oelprinz-org/BL49SP/software/V0.0.3_TEST/V0.0.3_TEST.ino

/*
    Example code compatible with the Lambda Shield for Arduino.
    
    Copyright (C) 2017 - 2020 Bylund Automotive AB.

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
    Contact information of author:
    http://www.bylund-automotive.com/
    
    info@bylund-automotive.com

    Version history:
    2020-03-29        v1.0.0        First release to GitHub.
    2020-06-18        v1.1.0        Implemented support for data logging.
    2023-12-18        v1.1.1        Adaption for BL49sp.

*/

//Define included headers.
#include <SPI.h>
#include <SD.h>
#include <Wire.h>
#include <Adafruit_MCP4725.h>

Adafruit_MCP4725 MCP4725;

//Define CJ125 registers used.
#define           CJ125_IDENT_REG_REQUEST             0x4800        /* Identify request, gives revision of the chip. */
#define           CJ125_DIAG_REG_REQUEST              0x7800        /* Dignostic request, gives the current status. */
#define           CJ125_INIT_REG1_REQUEST             0x6C00        /* Requests the first init register. */
#define           CJ125_INIT_REG2_REQUEST             0x7E00        /* Requests the second init register. */
#define           CJ125_INIT_REG1_MODE_CALIBRATE      0x569D        /* Sets the first init register in calibration mode. */
#define           CJ125_INIT_REG1_MODE_NORMAL_V8      0x5688        /* Sets the first init register in operation mode. V=8 amplification. */
#define           CJ125_INIT_REG1_MODE_NORMAL_V17     0x5689        /* Sets the first init register in operation mode. V=17 amplification. */
#define           CJ125_DIAG_REG_STATUS_OK            0x28FF        /* The response of the diagnostic register when everything is ok. */
#define           CJ125_DIAG_REG_STATUS_NOPOWER       0x2855        /* The response of the diagnostic register when power is low. */
#define           CJ125_DIAG_REG_STATUS_NOSENSOR      0x287F        /* The response of the diagnostic register when no sensor is connected. */
#define           CJ125_INIT_REG1_STATUS_0            0x2888        /* The response of the init register when V=8 amplification is in use. */
#define           CJ125_INIT_REG1_STATUS_1            0x2889        /* The response of the init register when V=17 amplification is in use. */

//Define pin assignments.
#define           CJ125_NSS_PIN                       10            /* Pin used for chip select in SPI communication. */
#define           LED_STATUS_POWER                    7             /* Pin used for power the status LED, indicating we have power. */
#define           LED_STATUS_HEATER                   5             /* Pin used for the heater status LED, indicating heater activity. */
#define           HEATER_OUTPUT_PIN                   6             /* Pin used for the PWM output to the heater circuit. */
#define           ANALOG_OUTPUT_PIN                   3             /* Pin used for the PWM to the 0-1V analog output. */
#define           UB_ANALOG_INPUT_PIN                 A0            /* Analog input for power supply.*/
#define           UR_ANALOG_INPUT_PIN                 A6            /* Analog input for temperature.*/
#define           UA_ANALOG_INPUT_PIN                 A7            /* Analog input for lambda.*/
#define           EN_INPUT_PIN                      	16  	        /* Enable pin, low when engine running */

//Define adjustable parameters.
#define           SERIAL_RATE                         1             /* Serial refresh rate in HZ (1-100)*/                           
#define           UBAT_MIN                            150           /* Minimum voltage (ADC value) on Ubat to operate */

/* Define DAC MCP4725 address MCP4725A2T-E/CH */
#define DAC1_ADDR				                              0x60	        /* Address for DAC 1 chip A0 tied to GND */

/* Define DAC MCP4725 registers */
#define MCP4725_CMD_WRITEDAC			                    0x40	        /* Writes data to the DAC */
#define MCP4725_CMD_WRITEDACEEPROM		                0x60          /* Writes data to the DAC and the EEPROM (persisting the assigned value after reset) */

//Global variables.
int adcValue_UA = 0;                                                /* ADC value read from the CJ125 UA output pin */ 
int adcValue_UR = 0;                                                /* ADC value read from the CJ125 UR output pin */
int adcValue_UB = 0;                                                /* ADC value read from the voltage divider caluclating Ubat */
int adcValue_UA_Optimal = 0;                                        /* UA ADC value stored when CJ125 is in calibration mode, λ=1 */ 
int adcValue_UR_Optimal = 0;                                        /* UR ADC value stored when CJ125 is in calibration mode, optimal temperature */
int HeaterOutput = 0;                                               /* Current PWM output value (0-255) of the heater output pin */
int serial_counter = 0;                                             /* Counter used to calculate refresh rate on the serial output */
int CJ125_Status = 0;                                               /* Latest stored DIAG registry response from the CJ125 */
bool logEnabled = false;                                            /* Variable used for setting data logging enable or disabled. */
int MCP4725_value = 0;                                              /* Variable used for DAC output */


//PID regulation variables.
int dState;                                                         /* Last position input. */
int iState;                                                         /* Integrator state. */
const int iMax = 250;                                               /* Maximum allowable integrator state. */
const int iMin = -250;                                              /* Minimum allowable integrator state. */
const float pGain = 120;                                            /* Proportional gain. Default = 120*/
const float iGain = 0.8;                                            /* Integral gain. Default = 0.8*/
const float dGain = 10;                                             /* Derivative gain. Default = 10*/

//Lambda Conversion Lookup Table. (ADC 39-791).
const PROGMEM float Lambda_Conversion[753] {
  0.750, 0.751, 0.752, 0.752, 0.753, 0.754, 0.755, 0.755, 0.756, 0.757, 0.758, 0.758, 0.759, 0.760, 0.761, 0.761, 0.762, 0.763, 0.764, 0.764,
  0.765, 0.766, 0.766, 0.767, 0.768, 0.769, 0.769, 0.770, 0.771, 0.772, 0.772, 0.773, 0.774, 0.774, 0.775, 0.776, 0.777, 0.777, 0.778, 0.779,
  0.780, 0.780, 0.781, 0.782, 0.782, 0.783, 0.784, 0.785, 0.785, 0.786, 0.787, 0.787, 0.788, 0.789, 0.790, 0.790, 0.791, 0.792, 0.793, 0.793,
  0.794, 0.795, 0.796, 0.796, 0.797, 0.798, 0.799, 0.799, 0.800, 0.801, 0.802, 0.802, 0.803, 0.804, 0.805, 0.805, 0.806, 0.807, 0.808, 0.808,
  0.809, 0.810, 0.811, 0.811, 0.812, 0.813, 0.814, 0.815, 0.815, 0.816, 0.817, 0.818, 0.819, 0.820, 0.820, 0.821, 0.822, 0.823, 0.824, 0.825,
  0.825, 0.826, 0.827, 0.828, 0.829, 0.830, 0.830, 0.831, 0.832, 0.833, 0.834, 0.835, 0.836, 0.837, 0.837, 0.838, 0.839, 0.840, 0.841, 0.842,
  0.843, 0.844, 0.845, 0.846, 0.846, 0.847, 0.848, 0.849, 0.850, 0.851, 0.852, 0.853, 0.854, 0.855, 0.855, 0.856, 0.857, 0.858, 0.859, 0.860,
  0.861, 0.862, 0.863, 0.864, 0.865, 0.865, 0.866, 0.867, 0.868, 0.869, 0.870, 0.871, 0.872, 0.873, 0.874, 0.875, 0.876, 0.877, 0.878, 0.878,
  0.879, 0.880, 0.881, 0.882, 0.883, 0.884, 0.885, 0.886, 0.887, 0.888, 0.889, 0.890, 0.891, 0.892, 0.893, 0.894, 0.895, 0.896, 0.897, 0.898,
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
  14.34, 14.38, 14.41, 14.45, 14.49, 14.52, 14.56, 14.60, 14.64, 14.67, 14.71, 14.75, 14.78, 14.82, 14.86, 14.90, 14.93, 14.97, 15.01, 15.04,
  15.08, 15.12, 15.15, 15.19, 15.23, 15.26, 15.30, 15.34, 15.37, 15.41, 15.45, 15.48, 15.52, 15.56, 15.59, 15.63, 15.67, 15.70, 15.74, 15.78,
  15.81, 15.85, 15.89, 15.92, 15.96, 16.00, 16.03, 16.07, 16.11, 16.14, 16.18, 16.22, 16.25, 16.29, 16.32, 16.36, 16.40, 16.43, 16.47, 16.51,
  16.54, 16.58, 16.61, 16.65, 16.69, 16.72, 16.76, 16.79, 16.83, 16.87, 16.90, 16.94, 16.97, 17.01, 17.05, 17.08, 17.12, 17.15, 17.19, 17.22,
  17.26, 17.30, 17.33, 17.37, 17.40, 17.44, 17.47, 17.51, 17.55, 17.58, 17.62, 17.65, 17.69, 17.72, 17.76, 17.79, 17.83, 17.86, 17.90, 17.94,
  17.97, 18.01, 18.04, 18.08, 18.11, 18.15, 18.18, 18.22, 18.25, 18.29, 18.32, 18.36, 18.39, 18.43, 18.46, 18.50, 18.53, 18.57, 18.60, 18.64,
  18.67, 18.71, 18.74, 18.78, 18.81, 18.85, 18.88, 18.92, 18.95, 18.98, 19.02, 19.05, 19.09, 19.12, 19.16, 19.19, 19.23, 19.26, 19.30, 19.33,
  19.36, 19.40, 19.43, 19.47, 19.50, 19.54, 19.57, 19.60, 19.64, 19.67, 19.71, 19.74, 19.77, 19.81, 19.84, 19.88, 19.91, 19.94, 19.98, 20.01,
  20.05, 20.08, 20.11, 20.15, 20.18, 20.22, 20.25, 20.28, 20.32, 20.35, 20.38, 20.42, 20.45, 20.48, 20.52, 20.55, 20.58, 20.62, 20.65, 20.68,
  20.72, 20.75, 20.78, 20.82, 20.85, 20.88, 20.92, 20.95
};

//Function for transfering SPI data to the CJ125.
uint16_t COM_SPI(uint16_t TX_data) {

  //Configure SPI for CJ125 controller.
  SPI.setDataMode(SPI_MODE1);
  SPI.setClockDivider(SPI_CLOCK_DIV128);
  
  //Set chip select pin low, chip in use. 
  digitalWrite(CJ125_NSS_PIN, LOW);

  //Transmit request.
  uint16_t Response =  SPI.transfer16(TX_data);

  //Set chip select pin high, chip not in use.
  digitalWrite(CJ125_NSS_PIN, HIGH);

  return Response;
  
}

//Temperature regulating software (PID).
int Heater_PID_Control(int input) {
  
  //Calculate error term.
  int error = adcValue_UR_Optimal - input;
  
  //Set current position.
  int position = input;
  
  //Calculate proportional term.
  float pTerm = -pGain * error;
  
  //Calculate the integral state with appropriate limiting.
  iState += error;
  
  if (iState > iMax) iState = iMax;
  if (iState < iMin) iState = iMin;
  
  //Calculate the integral term.
  float iTerm = -iGain * iState;
  
  //Calculate the derivative term.
  float dTerm = -dGain * (dState - position);
  dState = position;
  
  //Calculate regulation (PI).
  int RegulationOutput = pTerm + iTerm + dTerm;
  
  //Set maximum heater output (full power).
  if (RegulationOutput > 255) RegulationOutput = 255;
  
  //Set minimum heater value (cooling).
  if (RegulationOutput < 0.0) RegulationOutput = 0;

  //Return calculated PWM output.
  return RegulationOutput;
  
}

//Displays the AFR value on an external narrowband lambda gauge with an (RC-filtered) 0-1V PWM signal from ANALOG_OUTPUT_PIN. 0V = AFR 20.00. 1V = AFR 10.00.
//Also writes the AFR value to the MCP4725 DAC. 0V = AFR 10.00. 5V = AFR 20.00.
void UpdateAnalogOutput() {

  //Local constants.
  const float AirFuelRatioOctane = 14.70;
  const int maximumOutput = 51; /* maximum Voltage for narrowband output 1V */
  const int minimumOutput = 0;  /* minimum Voltage for narrowband output 0V */
  const int dacminimumOutput = 0;  /* minimum Voltage for wideband output 0V */
  const int dacmaximumOutput = 4095; /* maximum Voltage for wideband output 5V */

  //Local variables.
  int analogOutput = 0;
  int MCP4725_value = 0;

  float lambdaAFR = Lookup_Lambda(adcValue_UA) * AirFuelRatioOctane;

  //Convert lambda value to PWM output.
  analogOutput = map(lambdaAFR * 100, 1000, 2000, minimumOutput, maximumOutput);

  //Make sure we do not exceed maximum values.
  if (analogOutput > maximumOutput) analogOutput = maximumOutput;
  if (analogOutput < minimumOutput) analogOutput = minimumOutput;
  
  //Set PWM analog output.
  analogWrite(ANALOG_OUTPUT_PIN, analogOutput);

  //Convert lambda value to dac output.
  MCP4725_value = map(lambdaAFR * 100, 1000, 2000, dacminimumOutput, dacmaximumOutput);

  //Make sure we do not exceed maximum values.
  if (MCP4725_value > dacmaximumOutput) MCP4725_value = dacmaximumOutput;
  if (MCP4725_value < dacminimumOutput) MCP4725_value = dacminimumOutput;
  
  //Set dac output.
  /////MCP4725_value = (Lookup_Lambda(adcValue_UA) - 0,68) * 6022,058823529412;
  MCP4725.setVoltage(MCP4725_value, false);



}

//Lookup Lambda Value.
float Lookup_Lambda(int Input_ADC) {
  
    //Declare and set default return value.
    float LAMBDA_VALUE = 0;

    //Validate ADC range for lookup table.
    if (Input_ADC >= 39 && Input_ADC <= 791) {
      LAMBDA_VALUE = pgm_read_float_near(Lambda_Conversion + (Input_ADC-39));
    }
    
    if (Input_ADC > 791) {
      LAMBDA_VALUE = 10.119;
    }

    if (Input_ADC < 39) {
      LAMBDA_VALUE = 0.750;
    }
    
    //Return value.
    return LAMBDA_VALUE;
    
}

//Lookup Oxygen Content.
float Lookup_Oxygen(int Input_ADC) {
  
    //Declare and set default return value.
    float OXYGEN_CONTENT = 0;

    //Validate ADC range for lookup table.
    if (Input_ADC > 854) Input_ADC = 854;
    
    if (Input_ADC >= 307 && Input_ADC <= 854) {
      OXYGEN_CONTENT = pgm_read_float_near(Oxygen_Conversion + (Input_ADC - 307));
    }
    
    //Return value.
    return OXYGEN_CONTENT;
    
}

//Data logging function.
void logData(String logString) {

  //Connect to SD-Card.
  if ( SD.begin() ) {

    //Open file.
    File logFile = SD.open("log.txt", FILE_WRITE);

    //Store data.
    logFile.println(logString);

    //Close file.
    logFile.close();

    //Flush SPI, required when switching between modes.
    COM_SPI(0x00);
    
  } else {
    
    //Error handling.
    Serial.println("Error accessing SD-card.");  
    
  }
  
}

//Function to set up device for operation.
void setup() {

  // Set up MCP4725 address
  MCP4725.begin(DAC1_ADDR);
  
  //Set up serial communication.
  Serial.begin(9600);

  //Set up SPI.
  SPI.begin();  /* Note, SPI will disable the bult in LED. */
  SPI.setBitOrder(MSBFIRST);

  //Set up digital output pins.
  pinMode(CJ125_NSS_PIN, OUTPUT);  
  pinMode(LED_STATUS_POWER, OUTPUT);
  pinMode(LED_STATUS_HEATER, OUTPUT);
  pinMode(HEATER_OUTPUT_PIN, OUTPUT);

  //Set initial values.
  digitalWrite(CJ125_NSS_PIN, HIGH);
  digitalWrite(LED_STATUS_POWER, LOW);
  digitalWrite(LED_STATUS_HEATER, LOW);
  analogWrite(HEATER_OUTPUT_PIN, 0); /* PWM is initially off. */
  analogWrite(ANALOG_OUTPUT_PIN, 0); /* PWM is initially off. */
    
  //Start of operation. (Test LED's).
  Serial.print("Device reset.\n\r");
  digitalWrite(LED_STATUS_POWER, HIGH);
  digitalWrite(LED_STATUS_HEATER, HIGH);
  delay(200);
  digitalWrite(LED_STATUS_POWER, LOW);
  digitalWrite(LED_STATUS_HEATER, LOW);

  //Configure data logging.
  if ( SD.begin() ) {
    
    //Enable data logging.
    Serial.println("Data logging enabled.");
    logEnabled = true;

    //Flush SPI, required when switching between modes.
    COM_SPI(0x00);
    
  }
  
  //Start main function.
  start();

}

void start() {
  
  //Wait until everything is ready.
  while (adcValue_UB < UBAT_MIN || CJ125_Status != CJ125_DIAG_REG_STATUS_OK) {
    
    //Read CJ125 diagnostic register from SPI.
    CJ125_Status = COM_SPI(CJ125_DIAG_REG_REQUEST);

    //Error handling.
    if (CJ125_Status != CJ125_DIAG_REG_STATUS_OK) {
      Serial.print("Error, CJ125: 0x");
      Serial.print(CJ125_Status, HEX);
      Serial.print("\n\r");
    }
    
    //Read input voltage.
    adcValue_UB = analogRead(UB_ANALOG_INPUT_PIN);

    delay(1000);
  }

  //Start of operation. (Start Power LED).
  Serial.print("Device ready.\n\r");
  digitalWrite(LED_STATUS_POWER, HIGH);

  //Store calibrated optimum values.
  Serial.print("Reading calibration data.\n\r");

  //Set CJ125 in calibration mode.
  COM_SPI(CJ125_INIT_REG1_MODE_CALIBRATE);

  //Let values settle.
  delay(500);

  //Store optimal values before leaving calibration mode.
  adcValue_UA_Optimal = analogRead(UA_ANALOG_INPUT_PIN);
  adcValue_UR_Optimal = analogRead(UR_ANALOG_INPUT_PIN);
  
  //Update analog output, display the optimal value.
  adcValue_UA = adcValue_UA_Optimal;
  UpdateAnalogOutput();
    
  //Set CJ125 in normal operation mode.
  //COM_SPI(CJ125_INIT_REG1_MODE_NORMAL_V8);  /* V=0 */
  COM_SPI(CJ125_INIT_REG1_MODE_NORMAL_V17);  /* V=1 */

  //Present calibration data:
  Serial.print("UA_Optimal (λ = 1.00): ");
  Serial.print(adcValue_UA_Optimal);
  Serial.print(" (λ = ");
  Serial.print(Lookup_Lambda(adcValue_UA_Optimal), 2);
  Serial.print(")\n\r");
  Serial.print("UR_Optimal: ");
  Serial.print(adcValue_UR_Optimal);
  Serial.print("\n\r");
  
  /* Heat up sensor. This is described in detail in the datasheet of the LSU 4.9 sensor with a 
   * condensation phase and a ramp up face before going in to PID control. */
  Serial.print("Heating sensor.\n\r");    

  //Calculate supply voltage.
  float SupplyVoltage = (((float)adcValue_UB / 1023 * 5) / 10000) * 110000;

  //Condensation phase, 2V for 5s.
  int CondensationPWM = (2 / SupplyVoltage) * 255;
  analogWrite(HEATER_OUTPUT_PIN, CondensationPWM);

  int t = 0;
  while (t < 5 && analogRead(UB_ANALOG_INPUT_PIN) > UBAT_MIN) {

    //Flash Heater LED in condensation phase.
    digitalWrite(LED_STATUS_HEATER, HIGH);  
    delay(500);
          
    digitalWrite(LED_STATUS_HEATER, LOW);
    delay(500);

    t += 1;
    
  }

  //Ramp up phase, +0.4V / s until 100% PWM from 8.5V.
  float UHeater = 8.5;
  while (UHeater < 13.0 && analogRead(UB_ANALOG_INPUT_PIN) > UBAT_MIN) {

    //Set heater output during ramp up.
    CondensationPWM = (UHeater / SupplyVoltage) * 255;
      
    if (CondensationPWM > 255) CondensationPWM = 255; /*If supply voltage is less than 13V, maximum is 100% PWM*/

    analogWrite(HEATER_OUTPUT_PIN, CondensationPWM);

    //Flash Heater LED in condensation phase.
    digitalWrite(LED_STATUS_HEATER, HIGH);
    delay(500);
      
    digitalWrite(LED_STATUS_HEATER, LOW);
    delay(500);

    //Increment Voltage.
    UHeater += 0.4;
      
  }

  //Heat until temperature optimum is reached or exceeded (lower value is warmer).
  while (analogRead(UR_ANALOG_INPUT_PIN) > adcValue_UR_Optimal && analogRead(UB_ANALOG_INPUT_PIN) > UBAT_MIN) {

    //Flash Heater LED in condensation phase.
    digitalWrite(LED_STATUS_HEATER, HIGH);
    delay(500);
      
    digitalWrite(LED_STATUS_HEATER, LOW);
    delay(500);

  }

  //Heating phase finished, hand over to PID-control. Turn on LED and turn off heater.
  digitalWrite(LED_STATUS_HEATER, HIGH);
  analogWrite(HEATER_OUTPUT_PIN, 0);
  
}

//Infinite loop.
void loop() {

  //Update CJ125 diagnostic register from SPI.
  CJ125_Status = COM_SPI(CJ125_DIAG_REG_REQUEST);

  //Update analog inputs.
  adcValue_UA = analogRead(UA_ANALOG_INPUT_PIN);
  adcValue_UR = analogRead(UR_ANALOG_INPUT_PIN);
  adcValue_UB = analogRead(UB_ANALOG_INPUT_PIN);

  //Adjust PWM output by calculated PID regulation.
  if (adcValue_UR < 500 || adcValue_UR_Optimal != 0 || adcValue_UB > UBAT_MIN) {
    
    //Calculate and set new heater output.
    HeaterOutput = Heater_PID_Control(adcValue_UR);
    analogWrite(HEATER_OUTPUT_PIN, HeaterOutput);
    
  } else {
    
    //Turn off heater if we are not in PID control.
    HeaterOutput = 0;
    analogWrite(HEATER_OUTPUT_PIN, HeaterOutput);
    
  }

  //If power is lost, "reset" the device.
  if (adcValue_UB < UBAT_MIN) {

    //Indicate low power.
    Serial.print("Low power.\n");

    //Turn of status LEDs.
    digitalWrite(LED_STATUS_POWER, LOW);
    digitalWrite(LED_STATUS_HEATER, LOW);

    //Re-start() and wait for power.
    start();
    
  }
  
  //Display on serial port at defined rate. Comma separate values, readable by frontends.
  if ( (100 / SERIAL_RATE) ==  serial_counter) {

    //Reset counter.
    serial_counter = 0;

    //Calculate Lambda Value.
    float LAMBDA_VALUE = Lookup_Lambda(adcValue_UA);
      
    //Calculate Oxygen Content.
    float OXYGEN_CONTENT = Lookup_Oxygen(adcValue_UA);

    //Update analog output.
    UpdateAnalogOutput();


    //Display information if no errors is reported.
    if (CJ125_Status == CJ125_DIAG_REG_STATUS_OK) {
      
      //Assembled data.
      String txString = "Measuring, CJ125: 0x";
      txString += String(CJ125_Status, HEX);
      txString += ", UA_ADC: ";
      txString += String(adcValue_UA, DEC);
      txString += ", UR_ADC: ";
      txString += String(adcValue_UR, DEC);
      txString += ", UB_ADC: ";
      txString += String(adcValue_UB, DEC);

      //Display / output analog lambda value unless out of range.
      if (adcValue_UA >= 39 && adcValue_UA <= 791) {
          MCP4725.setVoltage(MCP4725_value, false);
          txString += ", Lambda: ";
          txString += String(LAMBDA_VALUE, 2);
      } else {
          txString += ", Lambda: -";
      }

      //Display oxygen unless out of range.
      if (adcValue_UA >= 307) {
        txString += ", Oxygen: ";
        txString += String(OXYGEN_CONTENT, 2);
        txString += "%";
      } else {
        txString += ", Oxygen: -";
      }
      
      //Output string
      Serial.println(txString);

      //Log string.
      if (logEnabled == true) logData(txString);
      
    } else {
      
      //Error handling.
      switch(CJ125_Status) {

        case CJ125_DIAG_REG_STATUS_NOPOWER:
          Serial.print("Error, CJ125: 0x");
          Serial.print(CJ125_Status, HEX);
          Serial.print(" (No Power)\n\r");
        break;
  
        case CJ125_DIAG_REG_STATUS_NOSENSOR:
          Serial.print("Error, CJ125: 0x");
          Serial.print(CJ125_Status, HEX);
          Serial.print(" (No Sensor)\n\r");
        break;

        default:
          Serial.print("Error, CJ125: 0x");
          Serial.print(CJ125_Status, HEX);
          Serial.print("\n\r");
        
        }
        
    }

  }

  //Increment serial output counter and delay for next cycle. The PID requires to be responsive but we don't need to flood the serial port.
  serial_counter++;
  delay(10);

}
